owais12-lgtm/blahaj-go-brrr/images/image-2.png

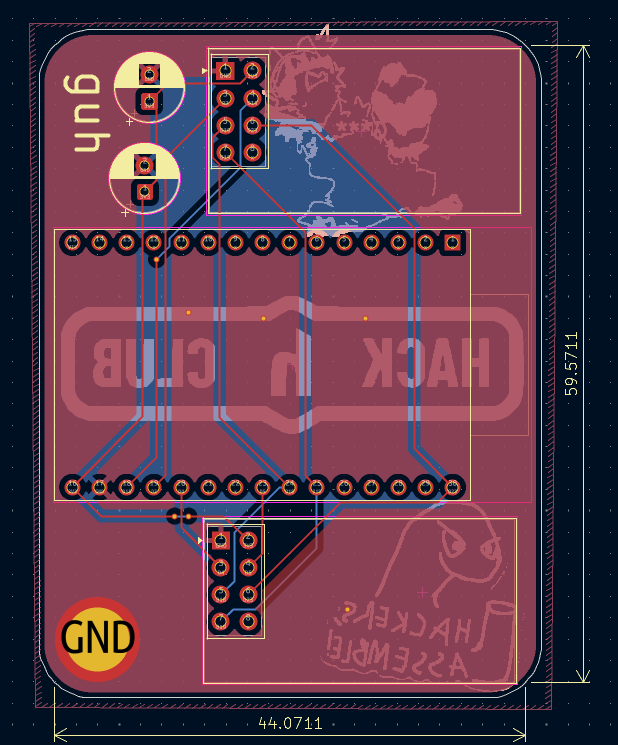
images/image-2.png
